karotka/sound.rail.crossing/src/pcm_sample.h

// const int pcm_sampleRate = 8000;
const int pcm_length = 6632;
//const int pcm_length = 1;

//const signed char pcm_samples[] PROGMEM ={122};

const signed char pcm_samples[] PROGMEM ={122,
134, 145, 130, 122, 117, 131, 132, 106, 117, 119, 131, 149, 129, 122, 120, 134, 134, 108, 106, 109,
144, 160, 131, 118, 107, 119, 129, 118, 119, 117, 134, 150, 133, 113, 97, 112, 129, 126, 128, 117,
124, 144, 136, 118, 100, 117, 138, 143, 140, 120, 131, 136, 124, 124, 103, 113, 131, 137, 141, 121,
120, 121, 126, 127, 109, 126, 135, 138, 147, 118, 113, 121, 129, 145, 125, 132, 138, 134, 141, 111,
101, 97, 117, 144, 117, 116, 117, 125, 136, 116, 116, 109, 131, 163, 136, 125, 119, 125, 134, 114,
120, 114, 125, 153, 133, 119, 105, 119, 131, 117, 130, 118, 129, 153, 137, 127, 105, 113, 136, 133,
145, 128, 123, 139, 132, 123, 98, 108, 130, 133, 147, 124, 109, 120, 120, 120, 105, 111, 132, 140,
144, 126, 115, 115, 122, 135, 112, 113, 131, 133, 143, 120, 104, 110, 122, 141, 131, 128, 132, 133,
143, 126, 112, 112, 128, 155, 139, 128, 125, 119, 132, 120, 114, 104, 113, 148, 137, 127, 117, 116,
128, 123, 127, 119, 127, 153, 149, 129, 107, 108, 119, 120, 126, 114, 112, 131, 131, 120, 97, 98,
118, 126, 138, 129, 118, 132, 135, 132, 111, 107, 131, 140, 152, 140, 124, 128, 134, 140, 116, 109,
126, 133, 150, 136, 115, 109, 113, 131, 120, 117, 129, 135, 149, 139, 121, 108, 117, 140, 135, 132,
132, 127, 136, 126, 109, 94, 104, 135, 131, 126, 116, 106, 119, 120, 117, 104, 112, 146, 152, 144,
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
135, 125, 117, 132, 134, 127, 127, 123, 132, 135, 135, 124, 108, 121, 129, 125, 122, 114, 121, 129,
132, 124, 108, 122, 135, 139, 139, 131, 133, 133, 138, 133, 111, 117, 130, 135, 133, 122, 121, 120,
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
